lastlxrd/Pogopo/docs/assets/gallery/gameboy-preview.gif

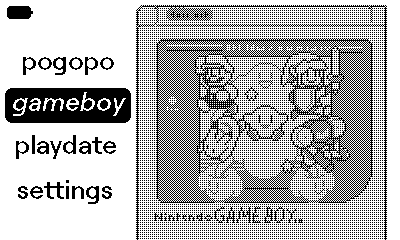
docs/assets/gallery/gameboy-preview.gif
