lastlxrd/Pogopo/docs/assets/gallery/launcher-states.png

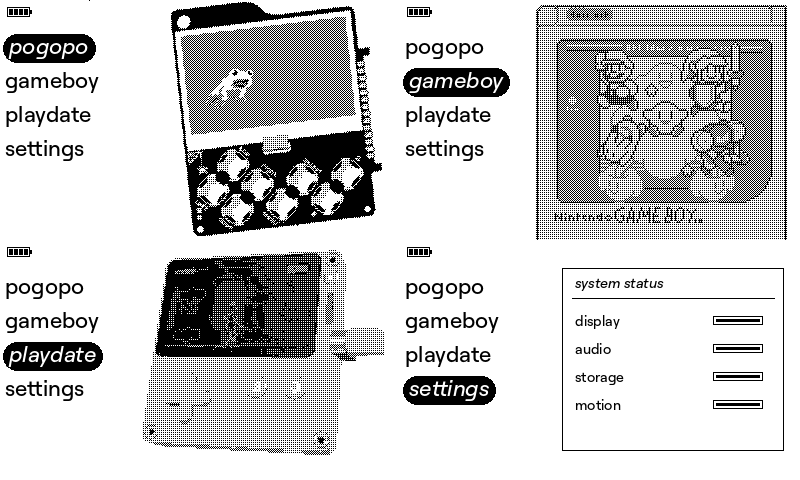
docs/assets/gallery/launcher-states.png
