lastlxrd/Pogopo/docs/assets/gallery/pcb-back.png

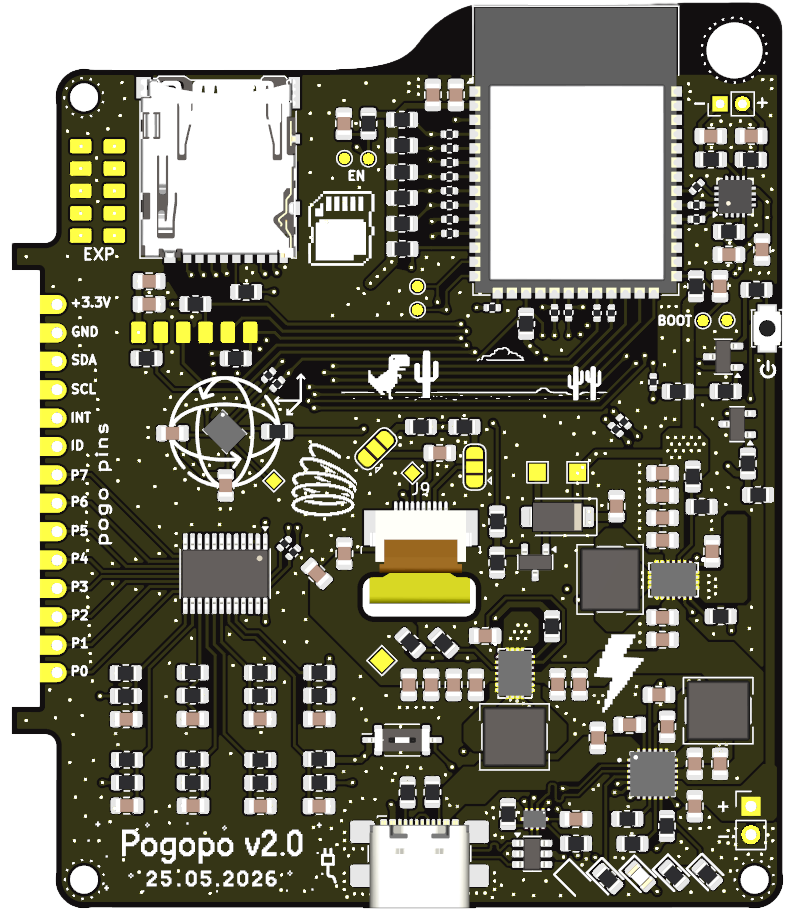
docs/assets/gallery/pcb-back.png
