lastlxrd/Pogopo/docs/assets/gallery/pcb-front.png

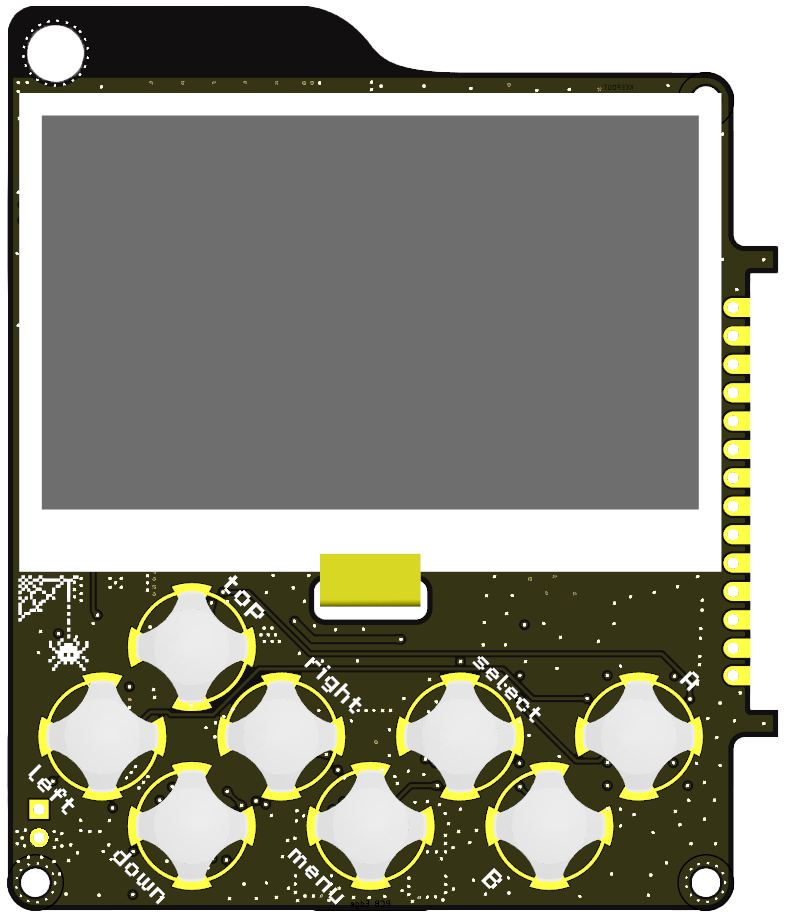
docs/assets/gallery/pcb-front.png
