lastlxrd/Pogopo/docs/assets/gallery/pogopo-preview.gif

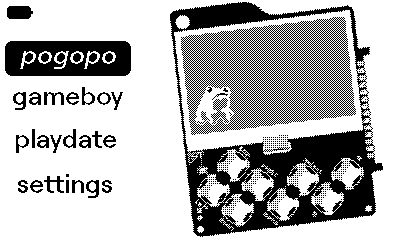
docs/assets/gallery/pogopo-preview.gif
