lastlxrd/Pogopo/docs/assets/gallery/quick-menu-clean.png

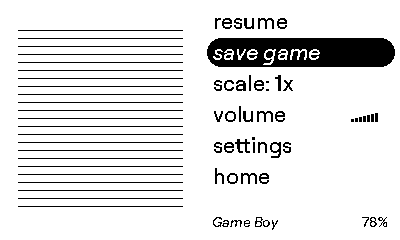
docs/assets/gallery/quick-menu-clean.png
