lastlxrd/Pogopo/docs/assets/gallery/quick-menu.png

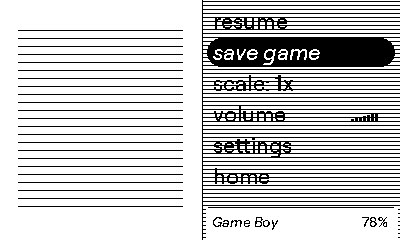
docs/assets/gallery/quick-menu.png
