lastlxrd/Pogopo/docs/assets/gallery/settings.png

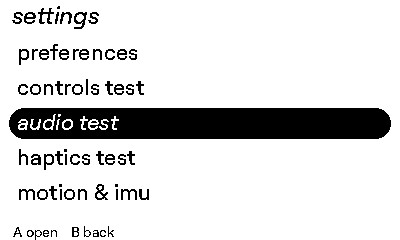
docs/assets/gallery/settings.png
