lastlxrd/Pogopo/docs/assets/gallery/startup.gif

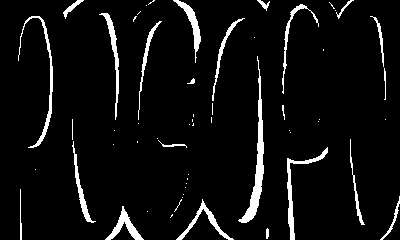
docs/assets/gallery/startup.gif
