lastlxrd/Pogopo/resourse/PCB/images pogopo/A.png

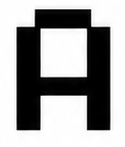
resourse/PCB/images pogopo/A.png
