lastlxrd/Pogopo/resourse/PCB/images pogopo/B.png

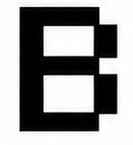
resourse/PCB/images pogopo/B.png
