lastlxrd/Pogopo/resourse/PCB/images pogopo/c.png

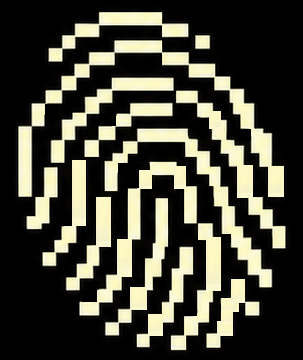
resourse/PCB/images pogopo/c.png
