lastlxrd/Pogopo/resourse/PCB/images pogopo/ChatGPT Image May 25, 2026, 04_06_45 PM.png

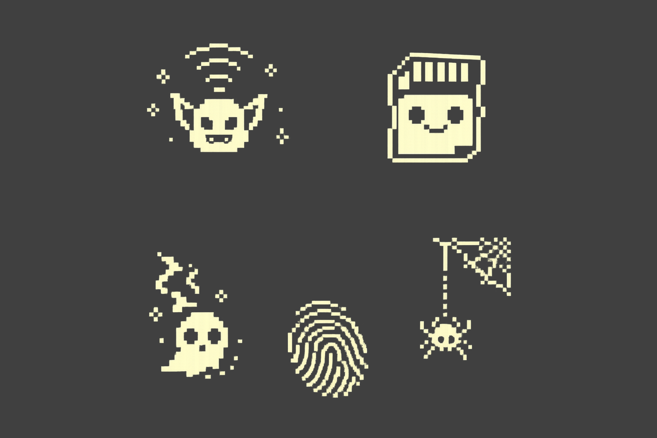
resourse/PCB/images pogopo/ChatGPT Image May 25, 2026, 04_06_45 PM.png
