lastlxrd/Pogopo/resourse/PCB/images pogopo/ChatGPT Image May 25, 2026, 04_35_06 PM.png

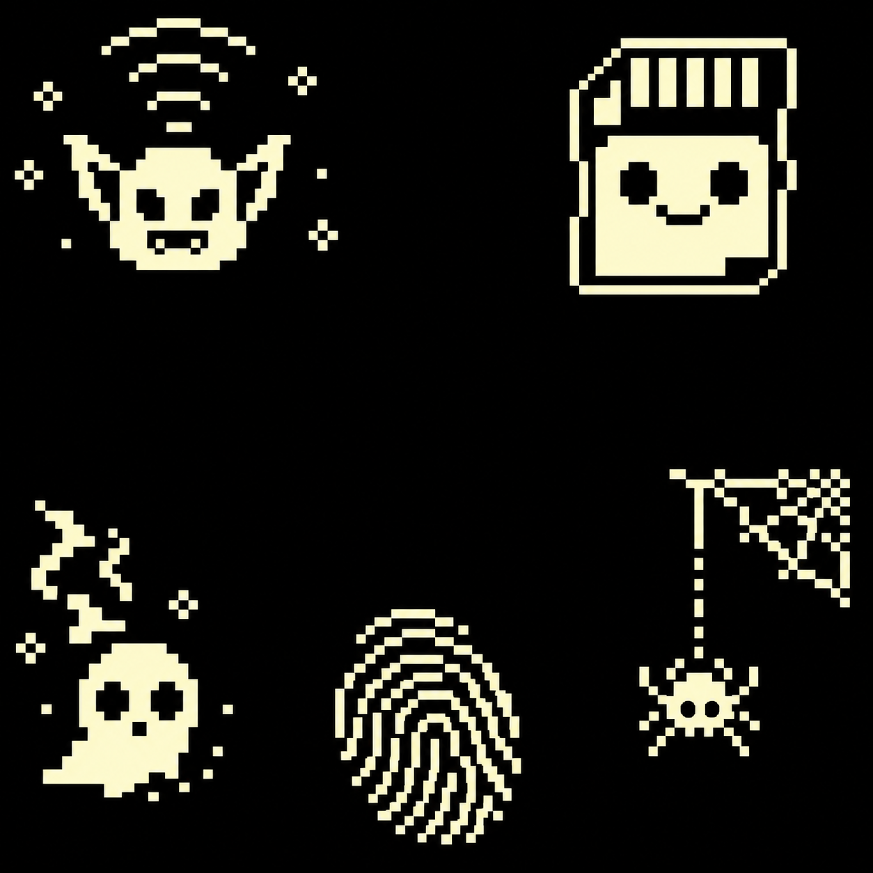
resourse/PCB/images pogopo/ChatGPT Image May 25, 2026, 04_35_06 PM.png
