lastlxrd/Pogopo/resourse/PCB/images pogopo/ChatGPT Image May 25, 2026, 05_19_58 PM.png

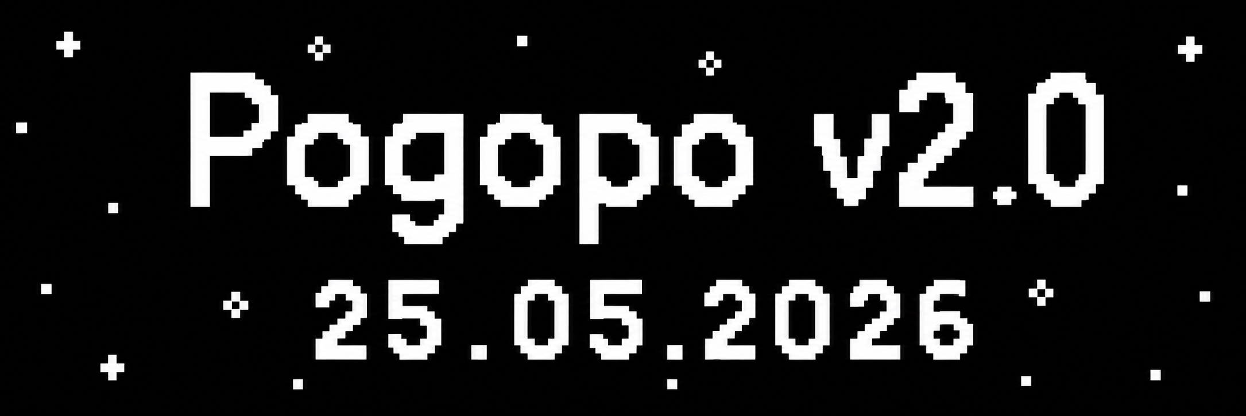
resourse/PCB/images pogopo/ChatGPT Image May 25, 2026, 05_19_58 PM.png
