lastlxrd/Pogopo/resourse/PCB/images pogopo/chrome-dino-hero.png

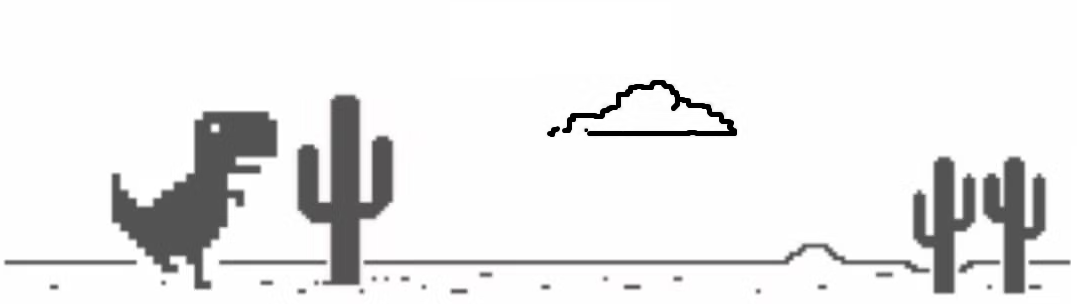
resourse/PCB/images pogopo/chrome-dino-hero.png
