lastlxrd/Pogopo/resourse/PCB/images pogopo/down.png

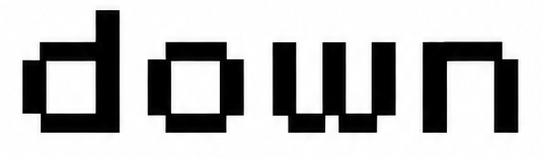
resourse/PCB/images pogopo/down.png
