lastlxrd/Pogopo/resourse/PCB/images pogopo/esp32.png

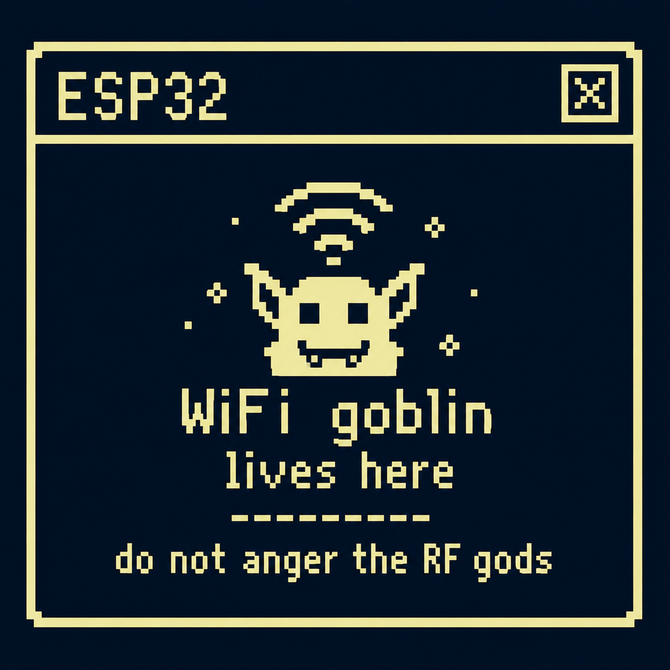
resourse/PCB/images pogopo/esp32.png
