lastlxrd/Pogopo/resourse/PCB/images pogopo/ghosti.png

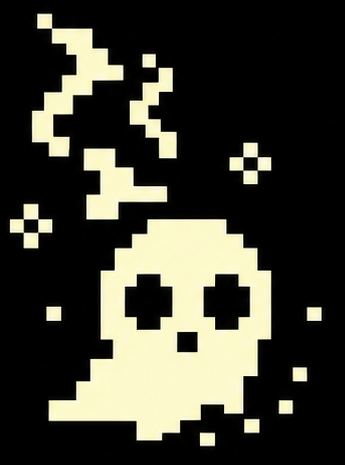
resourse/PCB/images pogopo/ghosti.png
