lastlxrd/Pogopo/resourse/PCB/images pogopo/gobl.png

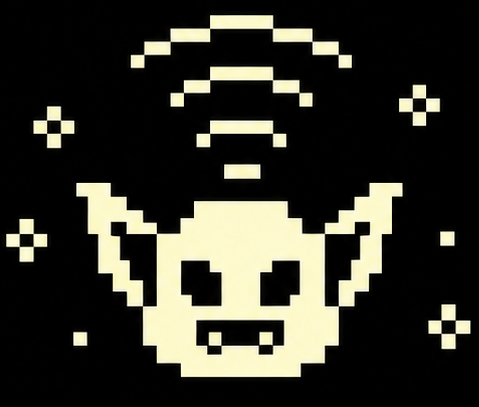
resourse/PCB/images pogopo/gobl.png
