lastlxrd/Pogopo/resourse/PCB/images pogopo/left.png

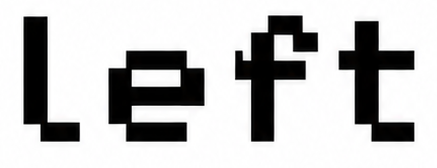
resourse/PCB/images pogopo/left.png
