lastlxrd/Pogopo/resourse/PCB/images pogopo/lightning.png

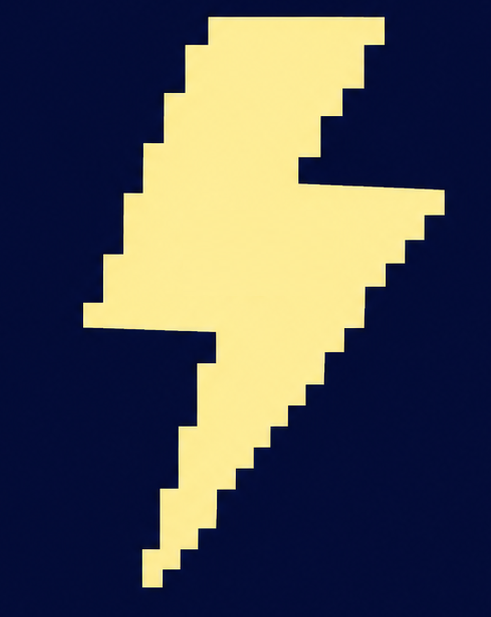
resourse/PCB/images pogopo/lightning.png
