lastlxrd/Pogopo/resourse/PCB/images pogopo/noise.png

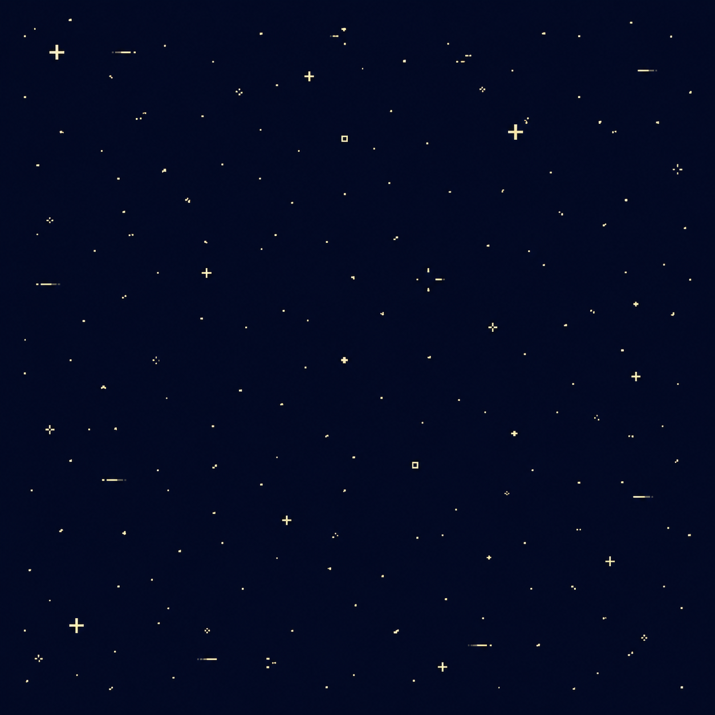
resourse/PCB/images pogopo/noise.png
