lastlxrd/Pogopo/resourse/PCB/images pogopo/pogopo.png

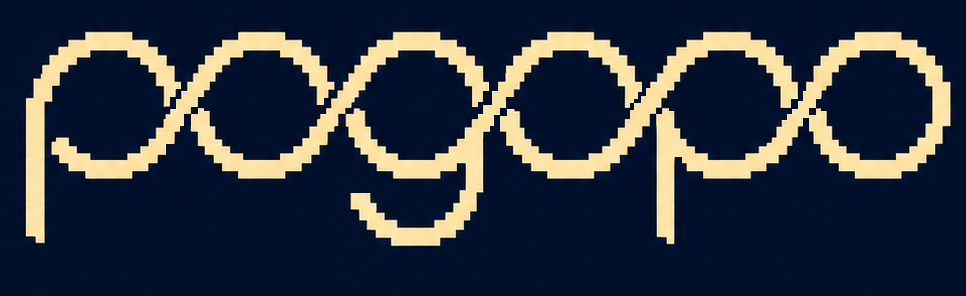
resourse/PCB/images pogopo/pogopo.png
