lastlxrd/Pogopo/resourse/PCB/images pogopo/pogos.png

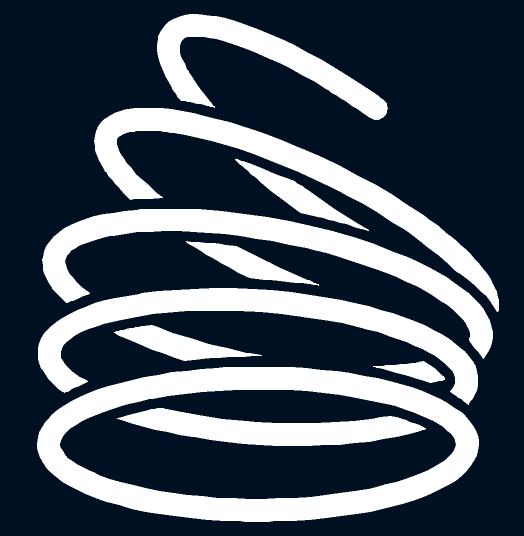
resourse/PCB/images pogopo/pogos.png
