lastlxrd/Pogopo/resourse/PCB/images pogopo/right.png

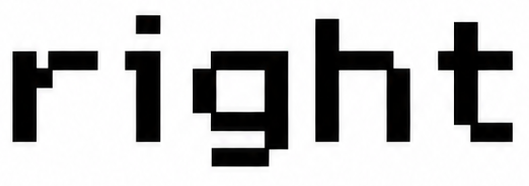
resourse/PCB/images pogopo/right.png
