lastlxrd/Pogopo/resourse/PCB/images pogopo/sdcard.png

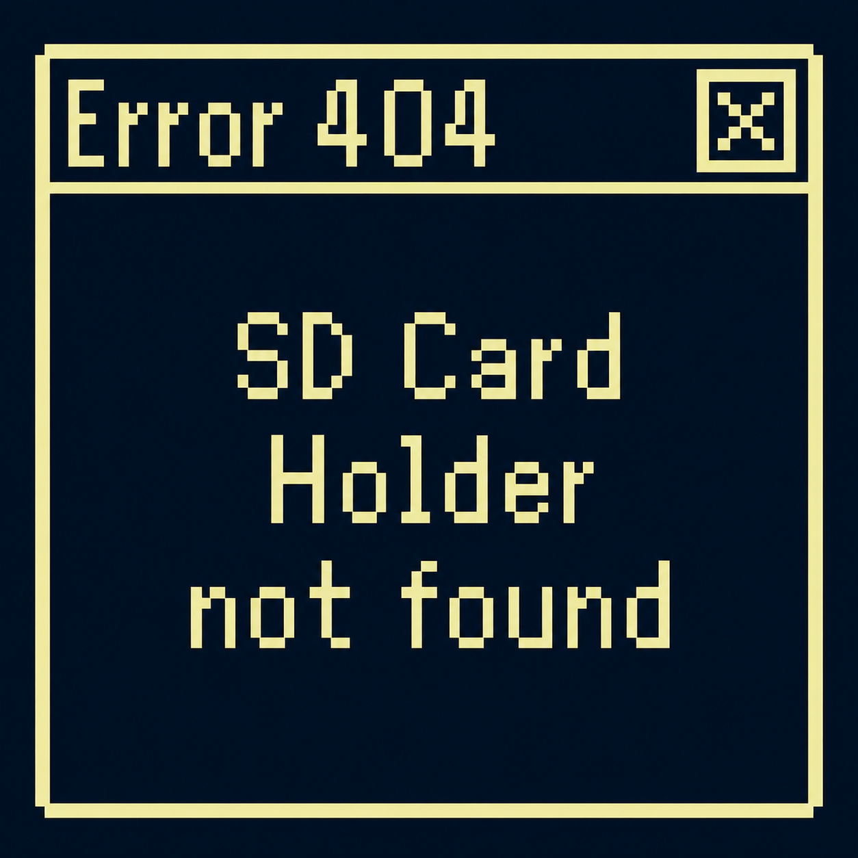
resourse/PCB/images pogopo/sdcard.png
