lastlxrd/Pogopo/resourse/PCB/images pogopo/sdcardd.png

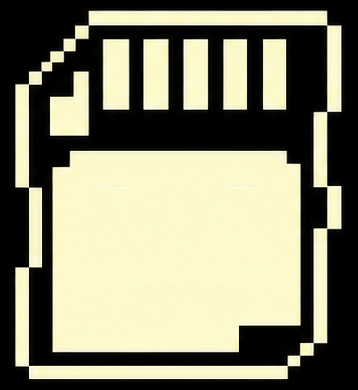
resourse/PCB/images pogopo/sdcardd.png
