lastlxrd/Pogopo/resourse/PCB/images pogopo/smokeghost.png

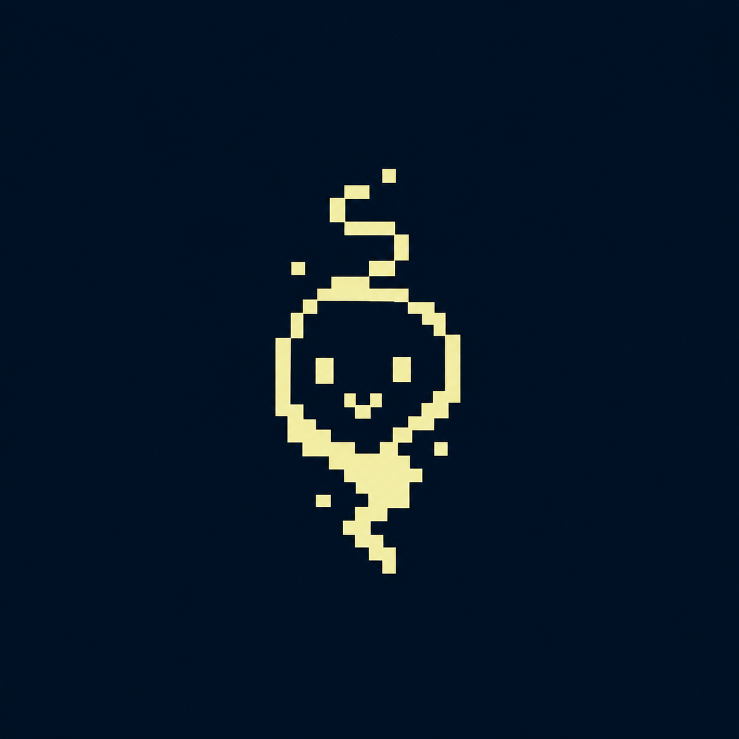
resourse/PCB/images pogopo/smokeghost.png
