lastlxrd/Pogopo/resourse/PCB/images pogopo/top.png

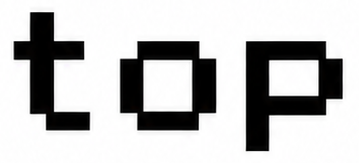
resourse/PCB/images pogopo/top.png
