lastlxrd/Pogopo/resourse/PCB/images pogopo/vapyk.png

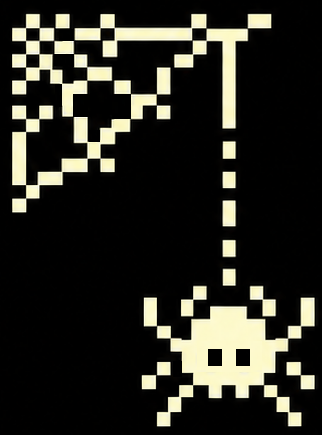
resourse/PCB/images pogopo/vapyk.png
