lastlxrd/Pogopo/resourse/PCB/images pogopo/wifi.png

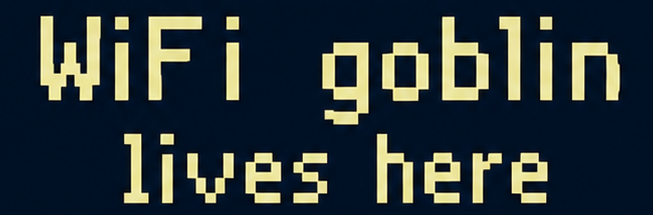
resourse/PCB/images pogopo/wifi.png
