lastlxrd/Pogopo/pogopoOS/components/pogopo_gameboy/THIRD_PARTY.md

# Third-party emulator core

- `peanut_gb.h`: Peanut-GB by Mahyar Koshkouei, MIT License. The complete license text is preserved at the top of the source file.
- `minigb_apu.c/.h`: MiniGB APU by Mahyar Koshkouei and Alex Baines, MIT License. Copyright notices are preserved in the source and the full text is in `third_party/LICENSE.minigb_apu`.

Pogopo's frontend, tasking, display scaling, SD loading, save handling, input mapping, and audio ring integration are project-specific code.
