lastlxrd/Pogopo/docs/history/11.6.23.md

# STEP11.6.23 — Hillslide gameplay timers and compact PDT frames

## Before

STEP11.6.22 let Hillslide open every scene and fixed the menu SFX player API.
On hardware, entering gameplay then consumed almost all remaining PSRAM: free
PSRAM fell from about 3.56 MiB to 0.87 MiB, Lua heap grew from 3.02 MiB to
4.85 MiB and individual logic updates took 1.1–3.1 seconds. After the surfer
briefly appeared, a trick timer stopped the game at `Game/Player.lua:619` with
`table.concat()` receiving nil instead of the player's combo table.

## Cause

The SDK form `playdate.timer.new(duration, callback, ...)` forwards every
explicit argument to the callback. Hillslide creates its timer as
`timer.new(400, self.doTrick, self)`. PogoDate discarded that `self` argument
and always passed the timer object, so `Player.doTrick()` operated on the wrong
table.

PDT image tables had two independent problems. PogoDate reported every table
as `frameCount x 1`, although the decompressed PDT header stores the real
column count. Hillslide's Idle table is `7 x 24`, not `168 x 1`; the wrong
shape selected unrelated surfer frames and angles.

PogoDate also inflated every PDT in full as soon as the gameplay scene was
created, then expanded requested frames to byte-per-pixel full canvases. The
21 Hillslide art tables total 1,288,358 bytes on SD but 3,810,052 bytes fully
inflated. Avalanche frames are 600 x 240, so caching them as full canvases
added another 144 KiB per frame.

## Changes

- preserve timer callback varargs in the timer object and forward them in
  order; a callback without explicit arguments still receives the timer;
- read PDT column count and return the real `(columns, rows)` from `getSize()`;
- retain the packed PDT stream instead of all inflated table bytes;
- inflate into one bounded transient buffer only when a previously unseen
  frame is requested, then free the buffer immediately;
- retain each decoded frame in its native trimmed 1-bit serialized form rather
  than allocating a byte for every transparent canvas pixel;
- bound each table's internal frame cache to 48 entries while preserving any
  image explicitly retained by Lua game code;
- materialize a compact frame to mutable pixels only if a game clears it or
  uses it as a graphics context;
- free external packed buffers from the image-table garbage collector.

## Result

A dedicated timer regression proves both callback forms: explicit object
arguments and the no-argument timer-object fallback. Real Hillslide probes
confirm Idle `7 x 24`, Avalanche `13 x 1`, mutable table-frame behaviour and
the corrected animation indexing.

The host run drives menu input, 500 Training frames and 1,000 main-game frames,
including trick timers, with zero Lua errors. Captured gameplay frames show a
properly indexed surfer and terrain. The theoretical persistent PDT payload
falls by about 2.52 MiB before counting the additional saving from compact
frames. Final PSRAM, frame time and SD/zlib cost still require the Pogopo
hardware check.

Menu input, callable scenes, font families, game compatibility, deep SFX,
Maze, Duel Of Shadows, input responder, synth and WOOD regressions pass. WOOD
keeps all eight previous progression checksums.
