lastlxrd/Pogopo/docs/history/11.6.4.md

# STEP11.6.4 — Maze gameplay and Duel boss-room compatibility

## Before

STEP11.6.3 fixed Noble dithering and frame-timer overloads, but Maze and Duel Of Shadows still exposed additional gameplay-time compatibility gaps beyond their startup and menu paths.

## Changes

Maze gained the remaining Noble/CoreLib, graphics, mask, accelerometer and collision support needed to enter gameplay, while Duel Of Shadows gained correct sprite defaults, scaling and draw-offset behavior required to reach and survive its boss room. :contentReference[oaicite:0]{index=0}

## Result

Maze now completes a 900-frame gameplay stress test with zero Lua errors, and Duel Of Shadows completes an 1800-frame boss-room, death, save and return regression with zero Lua errors.
