lastlxrd/Pogopo/docs/history/11.6.6.md

# STEP11.6.6 — Maze hole, correct BMI270 tilt and Duel portal

## Before

STEP11.6.5 fixed Maze Gridview and improved motion input, but Maze still failed during the ball-in-hole transition and Duel Of Shadows could miss its tutorial portal during a dash.

## Changes

Playdate image scaling, draw modes, masks and image-table APIs were expanded, the BMI270 Z axis was corrected for Playdate coordinates, and sprite overlap queries were separated from collision response so Duel's portal detection works during dashes. :contentReference[oaicite:0]{index=0}

## Result

Maze now completes the LevelComplete path with zero Lua errors, while Duel Of Shadows crosses the tutorial portal and continues into the boss room and combat successfully.
