lastlxrd/Pogopo/docs/history/11.6.md

# STEP11.6 — Broader Lua PDX compatibility validated with Duel Of Shadows

## Before

STEP11.5.1 corrected Playdate colors and LCD diagnostics, but more complex Lua PDX packages still exposed missing runtime APIs.

## Changes

The compatibility layer was expanded with JSON loading, font families, compiled resource-path resolution, tilemap sprites, timers, easing, additional audio formats and external PDZ module imports required by Duel Of Shadows. :contentReference[oaicite:0]{index=0}

## Result

Duel Of Shadows now boots from SD, enters gameplay, renders its room and assets, handles movement and attacks, and completes an 1800-frame host stress test with zero errors.
