lastlxrd/Pogopo/docs/history/13.1.md

# STEP13.1 — Menu polish and Playdate-style quick panel

## Before

STEP13.0 introduced the first complete animated Pogopo menu, but launcher spacing, console transitions, settings readability, ROM-browser response and the quick menu still needed refinement.

## Changes

The launcher layout and Game Boy/Playdate transitions were polished, Settings was simplified, ROM-browser redraws were optimized and a Playdate-style Power quick panel with Game Boy-specific actions was added. :contentReference[oaicite:0]{index=0}

## Result

The menu now feels more complete and responsive while preserving the existing startup, Game Boy core, audio, power handling and Sharp LCD presentation.
