lastlxrd/Pogopo/docs/history/13.0.md

# STEP13.0 — Animated menu revision 1

## Before

STEP12.4 provided the short interactive startup but still opened the old development launcher.

## Changes

The launcher was replaced with the first complete animated Pogopo menu using Pogofont, platform artwork, animated transitions, library pages, battery status and a redesigned Settings diagnostics hub. :contentReference[oaicite:0]{index=0}

## Result

The console now boots into the first full Pogopo UI revision while preserving the existing Game Boy emulator, audio, quick menu, power handling and Sharp LCD behavior.
