lastlxrd/Pogopo/docs/history/12.3.md

# STEP12.3 — Refreshed SharpBit startup and white shutdown

## Before

STEP12.2 tested a black retained shutdown frame while the startup animation still used the previous 111-frame export.

## Changes

The startup animation was replaced with a new 122-frame export from SharpBit, while the stable all-white shutdown behavior and STEP12.1 linker setup were restored. :contentReference[oaicite:0]{index=0}

## Result

The console now plays frames 1–117 once, loops frames 118–122 until input, and clears the Sharp LCD to white before entering ship mode.
