lastlxrd/Pogopo/pogopoOS/main/apps/gameboy_apps.cpp

#include "apps/gameboy_apps.h"

#include <algorithm>
#include <cmath>
#include <cstdio>
#include <cstring>
#include <sys/stat.h>

#include "esp_log.h"
#include "esp_heap_caps.h"
#include "pogopo_menu.h"

namespace pogopo::demo {
namespace {
constexpr char TAG[] = "gb_apps";
constexpr uint32_t EXIT_HOLD_MS = 650;

bool navigation_event(const input::Event& event) {
    return event.type == input::EventType::Pressed ||
           event.type == input::EventType::Repeat;
}

void copy_text(char* destination, size_t capacity, const char* source) {
    if (!destination || capacity == 0) return;
    if (!source) {
        destination[0] = '\0';
        return;
    }
    const size_t count = std::min(capacity - 1U, std::strlen(source));
    std::memcpy(destination, source, count);
    destination[count] = '\0';
}

} // namespace

void GameBoyApp::prepare(const char* path, const char* display_name,
                         gameboy::ScaleMode scale) {
    copy_text(rom_path_, sizeof(rom_path_), path);
    copy_text(display_name_, sizeof(display_name_), display_name);
    scale_ = scale;
}

const char* GameBoyApp::quickActionLabel(size_t index) const {
    if (index == 0) return "save game";
    if (index == 1) {
        return scale_ == gameboy::ScaleMode::FitHeight ? "scale: fit" : "scale: 1x";
    }
    return "";
}

bool GameBoyApp::runQuickAction(AppContext&, size_t index) {
    if (index == 0) return emulator_.flushSave() == ESP_OK;
    if (index == 1) {
        scale_ = scale_ == gameboy::ScaleMode::FitHeight
            ? gameboy::ScaleMode::OneX : gameboy::ScaleMode::FitHeight;
        force_draw_ = true;
        return true;
    }
    return false;
}

void GameBoyApp::drawLoading(AppContext& context) {
    auto& canvas = context.gfx.canvas();
    context.gfx.reset_clip();
    canvas.clear(context.theme.background);
    gui::draw_header(canvas, context.theme, "GAME BOY", "LOADING");
    canvas.draw_rect(28, 54, 344, 118, context.theme.border);
    menu::PogoFont::drawText(canvas, 48, 68, "Peanut-GB / MiniGB APU",
                             menu::FontFace::Regular14,
                             context.theme.foreground);
    menu::PogoFont::drawText(canvas, 48, 94,
                             display_name_[0] ? display_name_ : "ROM",
                             menu::FontFace::Italic14,
                             context.theme.foreground);
    menu::PogoFont::drawText(canvas, 48, 130,
                             "Reading ROM + save RAM...",
                             menu::FontFace::Regular14,
                             context.theme.foreground);
    gui::draw_footer(canvas, context.theme, "PLEASE WAIT", gameboy::scale_mode_name(scale_));
    context.gfx.presentFull();
}

void GameBoyApp::onEnter(AppContext& context) {
    exit_hold_ms_ = 0;
    last_sequence_ = UINT32_MAX;
    force_draw_ = true;
    perf_elapsed_ms_ = 0;
    perf_previous_ = {};
    load_error_ = ESP_ERR_INVALID_ARG;

    context.audio.stopStream();
    drawLoading(context);

    if (rom_path_[0]) {
        load_error_ = emulator_.load(rom_path_);
    }
    if (load_error_ == ESP_OK) {
        context.haptics.play(haptics::Effect::Confirm);
        ESP_LOGI(TAG, "Game started: %s", emulator_.romTitle());
    } else {
        context.haptics.play(haptics::Effect::Alert);
        context.uiSound(audio::Effect::Error);
        ESP_LOGE(TAG, "Game load failed: %s (%s)", rom_path_, esp_err_to_name(load_error_));
    }
    context.invalidate();
}

void GameBoyApp::onExit(AppContext&) {
    emulator_.unload();
    exit_hold_ms_ = 0;
}

void GameBoyApp::onSuspend(AppContext&) {
    emulator_.setButtons({});
    emulator_.setPaused(true);
    exit_hold_ms_ = 0;
}

void GameBoyApp::onResume(AppContext&) {
    emulator_.setPaused(false);
    force_draw_ = true;
}

void GameBoyApp::onEvent(AppContext& context, const input::Event& event) {
    if (load_error_ != ESP_OK && event.type == input::EventType::Pressed &&
        event.button == input::Button::B) {
        context.haptics.play(haptics::Effect::Click);
        context.uiSound(audio::Effect::Back);
        context.launch("gb_browser");
    }
}

void GameBoyApp::updateButtons(AppContext& context) {
    const input::ButtonMask held = context.input.heldMask();
    gameboy::Buttons buttons;
    buttons.up = (held & input::mask(input::Button::Top)) != 0;
    buttons.down = (held & input::mask(input::Button::Down)) != 0;
    buttons.left = (held & input::mask(input::Button::Left)) != 0;
    buttons.right = (held & input::mask(input::Button::Right)) != 0;
    buttons.a = (held & input::mask(input::Button::A)) != 0;
    buttons.b = (held & input::mask(input::Button::B)) != 0;
    buttons.start = (held & input::mask(input::Button::Start)) != 0;
    buttons.select = (held & input::mask(input::Button::Menu)) != 0;
    emulator_.setButtons(buttons);
}

void GameBoyApp::update(AppContext& context, uint32_t dt_ms) {
    if (load_error_ != ESP_OK || !emulator_.loaded()) return;
    updateButtons(context);

    const input::ButtonMask exit_combo =
        input::mask(input::Button::B) | input::mask(input::Button::Start);
    if (context.input.comboHeld(exit_combo)) {
        exit_hold_ms_ = std::min<uint32_t>(EXIT_HOLD_MS, exit_hold_ms_ + dt_ms);
        if (exit_hold_ms_ >= EXIT_HOLD_MS) {
            context.haptics.play(haptics::Effect::Heavy);
            context.uiSound(audio::Effect::Back);
            context.launch("gb_browser");
            return;
        }
    } else {
        exit_hold_ms_ = 0;
    }

    const uint32_t sequence = emulator_.frameSequence();
    if (sequence != last_sequence_) {
        last_sequence_ = sequence;
        context.invalidate({0, 0, context.gfx.width(), context.gfx.height()});
    }

    perf_elapsed_ms_ += dt_ms;
    if (perf_elapsed_ms_ >= 1000U) {
        const gameboy::Stats now = emulator_.stats();
        const uint32_t emu_delta = now.emulated_frames - perf_previous_.emulated_frames;
        const uint32_t lcd_delta = now.displayed_frames - perf_previous_.displayed_frames;
        const uint32_t hit_delta = now.cache_hits - perf_previous_.cache_hits;
        const uint32_t miss_delta = now.cache_misses - perf_previous_.cache_misses;
        const uint32_t fill_us_delta = now.cache_fill_us - perf_previous_.cache_fill_us;
        const uint32_t drop_delta = now.audio_frames_dropped - perf_previous_.audio_frames_dropped;
        const audio::RealtimeInfo realtime = context.audio.realtimeInfo();
        ESP_LOGI(TAG,
                 "PERF emu=%lu lcd=%lu frame=%luus max=%luus ROM=%s arena=%lu "
                 "fb=%lu cache=%u:%lu/%lu miss_us=%lu audio=%lu/%lu under=%lu "
                 "over=%lu drop=%lu heap=%lu/%lu i2cerr=%lu",
                 static_cast<unsigned long>(emu_delta),
                 static_cast<unsigned long>(lcd_delta),
                 static_cast<unsigned long>(now.last_frame_us),
                 static_cast<unsigned long>(now.max_frame_us),
                 now.rom_in_arena ? "ARENA" : (now.rom_in_psram ? "PSRAM" : "INT"),
                 static_cast<unsigned long>(now.rom_arena_bytes),
                 static_cast<unsigned long>(now.frame_buffer_bytes),
                 static_cast<unsigned>(now.cache_pages),
                 static_cast<unsigned long>(hit_delta),
                 static_cast<unsigned long>(miss_delta),
                 static_cast<unsigned long>(fill_us_delta),
                 static_cast<unsigned long>(realtime.buffered_frames),
                 static_cast<unsigned long>(realtime.capacity_frames),
                 static_cast<unsigned long>(realtime.underruns),
                 static_cast<unsigned long>(realtime.overruns),
                 static_cast<unsigned long>(drop_delta),
                 static_cast<unsigned long>(heap_caps_get_free_size(
                     MALLOC_CAP_INTERNAL | MALLOC_CAP_8BIT)),
                 static_cast<unsigned long>(heap_caps_get_largest_free_block(
                     MALLOC_CAP_INTERNAL | MALLOC_CAP_8BIT)),
                 static_cast<unsigned long>(context.input.readErrors()));
        perf_previous_ = now;
        perf_elapsed_ms_ = 0;
    }
}

void GameBoyApp::draw(AppContext& context, const gfx::Rect&) {
    auto& canvas = context.gfx.canvas();
    if (load_error_ != ESP_OK) {
        canvas.clear_clip(context.theme.background);
        gui::draw_header(canvas, context.theme, "GAME BOY", "LOAD ERROR");
        canvas.draw_rect(25, 48, 350, 145, context.theme.border);
        menu::PogoFont::drawText(canvas, 43, 60, "Could not start ROM",
                                 menu::FontFace::Italic22,
                                 context.theme.foreground);
        menu::PogoFont::drawText(canvas, 43, 101, display_name_,
                                 menu::FontFace::Regular14,
                                 context.theme.foreground);
        menu::PogoFont::drawText(canvas, 43, 126,
                                 esp_err_to_name(load_error_),
                                 menu::FontFace::Italic14,
                                 context.theme.foreground);
        menu::PogoFont::drawText(canvas, 43, 153,
                                 "Only uncompressed .gb is supported",
                                 menu::FontFace::Regular14,
                                 context.theme.foreground);
        gui::draw_footer(canvas, context.theme, "B BACK", "CHECK SERIAL");
        return;
    }

    emulator_.drawLatest(canvas, scale_, force_draw_);
    force_draw_ = false;
}

void GameBoyBrowserApp::rescan(AppContext& context) {
    file_count_ = 0;
    for (auto& file : files_) file = {};
    for (auto& item : items_) item = {};
    for (auto& subtitle : subtitles_) subtitle.fill('\0');

    if (!context.storage.mounted()) {
        items_[0] = {"SD CARD NOT READY", "Mount failed", nullptr, false};
        list_.setItems(items_.data(), 1);
        copy_text(status_, sizeof(status_), "SD IS NOT MOUNTED");
        return;
    }

    char folder[192]{};
    const char* mount = context.storage.mountPoint();
    const size_t mount_length = std::strlen(mount);
    constexpr char suffix[] = "/gameboy";
    if (mount_length + sizeof(suffix) <= sizeof(folder)) {
        std::memcpy(folder, mount, mount_length);
        std::memcpy(folder + mount_length, suffix, sizeof(suffix));
        mkdir(folder, 0775);
    }

    file_count_ = context.storage.listFiles(
        "/gameboy", ".gb", files_.data(), files_.size());
    if (file_count_ == 0) {
        items_[0] = {"NO .GB ROMS FOUND", "Put files in /gameboy", nullptr, false};
        list_.setItems(items_.data(), 1);
        copy_text(status_, sizeof(status_), "FOLDER: /gameboy");
        return;
    }

    for (size_t i = 0; i < file_count_; ++i) {
        const uint32_t kib = files_[i].size / 1024U;
        std::snprintf(subtitles_[i].data(), subtitles_[i].size(),
                      "%lu KiB  DMG", static_cast<unsigned long>(kib));
        items_[i] = {files_[i].name, subtitles_[i].data(), files_[i].path, true};
    }
    list_.setItems(items_.data(), file_count_);
    list_.setSelected(0);

    std::snprintf(status_, sizeof(status_), "%u ROMS  %s",
                  static_cast<unsigned>(file_count_), gameboy::scale_mode_name(scale_));
}

void GameBoyBrowserApp::onEnter(AppContext& context) {
    list_.setRowHeight(29);
    rescan(context);
    enter_elapsed_ms_ = 0;
    redraw_elapsed_ms_ = 0;
    context.invalidate();
}

void GameBoyBrowserApp::launchSelected(AppContext& context) {
    if (file_count_ == 0 || list_.selected() >= file_count_) {
        context.haptics.play(haptics::Effect::Alert);
        context.uiSound(audio::Effect::Error);
        return;
    }
    const size_t selected = list_.selected();
    player_.prepare(files_[selected].path, files_[selected].name, scale_);
    context.haptics.play(haptics::Effect::Confirm);
    context.uiSound(audio::Effect::Confirm);
    context.launch("gameboy");
}

void GameBoyBrowserApp::onEvent(AppContext& context, const input::Event& event) {
    if (!navigation_event(event)) return;

    if (event.button == input::Button::Top && list_.move(-1)) {
        context.haptics.play(haptics::Effect::Tick);
        context.uiSound(audio::Effect::Tick);
        // The custom 382 px focus pill extends well beyond gui::List::bounds().
        // Repaint every browser row so the old black fill is cleared in the
        // same Sharp refresh instead of visibly trailing the new selection.
        context.invalidate({0, 32, 400, 178});
    } else if (event.button == input::Button::Down && list_.move(1)) {
        context.haptics.play(haptics::Effect::Tick);
        context.uiSound(audio::Effect::Tick);
        context.invalidate({0, 32, 400, 178});
    } else if (event.type == input::EventType::Pressed &&
               (event.button == input::Button::Left || event.button == input::Button::Right)) {
        scale_ = scale_ == gameboy::ScaleMode::FitHeight
            ? gameboy::ScaleMode::OneX
            : gameboy::ScaleMode::FitHeight;
        context.haptics.play(haptics::Effect::Tick);
        context.uiSound(audio::Effect::Tick);
        std::snprintf(status_, sizeof(status_), "%u ROMS  %s",
                      static_cast<unsigned>(file_count_), gameboy::scale_mode_name(scale_));
        context.invalidate();
    } else if (event.type == input::EventType::Pressed && event.button == input::Button::A) {
        launchSelected(context);
    } else if (event.type == input::EventType::Pressed && event.button == input::Button::Start) {
        rescan(context);
        context.haptics.play(haptics::Effect::Click);
        context.uiSound(audio::Effect::Click);
        context.invalidate();
    } else if (event.type == input::EventType::Pressed && event.button == input::Button::B) {
        context.haptics.play(haptics::Effect::Click);
        context.uiSound(audio::Effect::Back);
        context.home();
    }
}

void GameBoyBrowserApp::update(AppContext& context, uint32_t dt_ms) {
    const uint32_t previous_enter = enter_elapsed_ms_;
    enter_elapsed_ms_ = std::min<uint32_t>(enter_elapsed_ms_ + dt_ms, 330U);
    redraw_elapsed_ms_ += dt_ms;
    if (previous_enter < 330U && enter_elapsed_ms_ == 330U) {
        redraw_elapsed_ms_ = 0;
        context.invalidate();
    } else if (enter_elapsed_ms_ < 330U && redraw_elapsed_ms_ >= 32U) {
        redraw_elapsed_ms_ %= 32U;
        context.invalidate();
    } else if (enter_elapsed_ms_ >= 330U && redraw_elapsed_ms_ >= 500U) {
        redraw_elapsed_ms_ %= 500U;
        context.invalidate();
    }
}

void GameBoyBrowserApp::draw(AppContext& context, const gfx::Rect&) {
    auto& canvas = context.gfx.canvas();
    canvas.clear_clip(gfx::WHITE);
    const float raw_progress = std::clamp<float>(
        static_cast<float>(enter_elapsed_ms_) / 330.0f, 0.0f, 1.0f);
    const float progress = 1.0f - std::pow(1.0f - raw_progress, 3.0f);
    const int content_x = static_cast<int>(std::lround((1.0f - progress) * 400.0f));

    menu::PogoFont::drawText(canvas, 12 + content_x, -1, "gameboy",
                             menu::FontFace::Italic22);
    const power::State power = context.power.state();
    canvas.draw_rect(366, 8, 23, 10, gfx::BLACK);
    canvas.fill_rect(389, 11, 2, 4, gfx::BLACK);
    const int battery_level = power.battery_valid
        ? std::clamp<int>((power.battery_percent + 24) / 25, 0, 4) : 0;
    for (int segment = 0; segment < battery_level; ++segment) {
        canvas.fill_rect(368 + segment * 5, 10, 4, 6, gfx::BLACK);
    }

    const size_t count = file_count_ ? file_count_ : 1;
    const int selected = static_cast<int>(list_.selected());
    constexpr int visible_rows = 7;
    const int first = std::clamp(selected - 3, 0,
        std::max(0, static_cast<int>(count) - visible_rows));
    for (int visible = 0; visible < visible_rows && first + visible < static_cast<int>(count); ++visible) {
        const int item_index = first + visible;
        const int y = 35 + visible * 25;
        const bool focus = item_index == selected;
        const auto& item = items_[item_index];
        if (focus) {
            canvas.fill_rect(9 + content_x, y + 1, 382, 22, gfx::BLACK);
            canvas.fill_circle(20 + content_x, y + 12, 11, gfx::BLACK);
            canvas.fill_circle(379 + content_x, y + 12, 11, gfx::BLACK);
        }

        char label[64]{};
        std::snprintf(label, sizeof(label), "%s", item.label ? item.label : "");
        const menu::FontFace face = focus
            ? menu::FontFace::Italic14 : menu::FontFace::Regular14;
        while (label[0] && menu::PogoFont::textWidth(face, label) > 280) {
            const size_t length = std::strlen(label);
            if (length <= 3) break;
            label[length - 1] = '\0';
        }
        menu::PogoFont::drawText(canvas, 16 + content_x, y, label, face,
                                 focus ? gfx::WHITE : gfx::BLACK);

        if (file_count_ && item_index < static_cast<int>(file_count_)) {
            const char* subtitle = subtitles_[item_index].data();
            const int width = menu::PogoFont::textWidth(face, subtitle);
            menu::PogoFont::drawText(canvas, 383 - width + content_x, y, subtitle,
                                     face, focus ? gfx::WHITE : gfx::BLACK);
        }
    }

    menu::PogoFont::drawText(canvas, 13 + content_x, 205, status_,
                             menu::FontFace::Italic14);
    menu::PogoFont::drawText(canvas, 13 + content_x, 220,
                             "A play  B back  L/R scale  START rescan",
                             menu::FontFace::Regular14);
}

} // namespace pogopo::demo
