lastlxrd/Pogopo/pogopoOS/components/pogopo_audio/include/pogopo_audio.h

#pragma once
#include "pogopo/audio/audio.h"

namespace pogopo {
using Audio = audio::Audio;
using AudioEffect = audio::Effect;
using AudioWaveform = audio::Waveform;
using AudioStats = audio::Stats;
using AudioStreamState = audio::StreamState;
using AudioStreamInfo = audio::StreamInfo;
using audio::effect_name;
using audio::waveform_name;
using audio::stream_state_name;
} // namespace pogopo
