lastlxrd/Pogopo/pogopoOS/components/pogopo_input/include/pogopo_input.h

#pragma once
#include "pogopo/input/input.h"

namespace pogopo {
using Input = input::Input;
using Button = input::Button;
using ButtonMask = input::ButtonMask;
using InputEvent = input::Event;
using InputEventType = input::EventType;
using input::button_name;
using input::event_type_name;
using input::mask;
} // namespace pogopo
